michaelhany41/Garbage-Bin-/2D drawing/download.jpeg

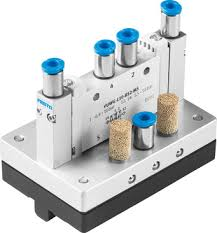
2D drawing/download.jpeg
