michaelhany41/Garbage-Bin-/SolidWorks design/Pneumatic Air Cylinder Double Action/1.jpg

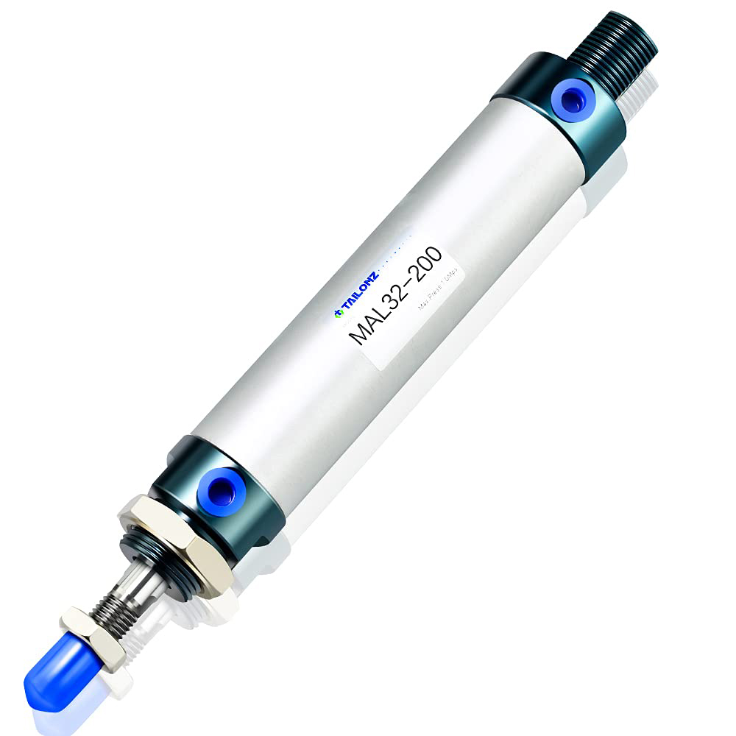
SolidWorks design/Pneumatic Air Cylinder Double Action/1.jpg
