michaelhany41/Garbage-Bin-/SolidWorks design/Pneumatic Air Cylinder Double Action/2.jpg

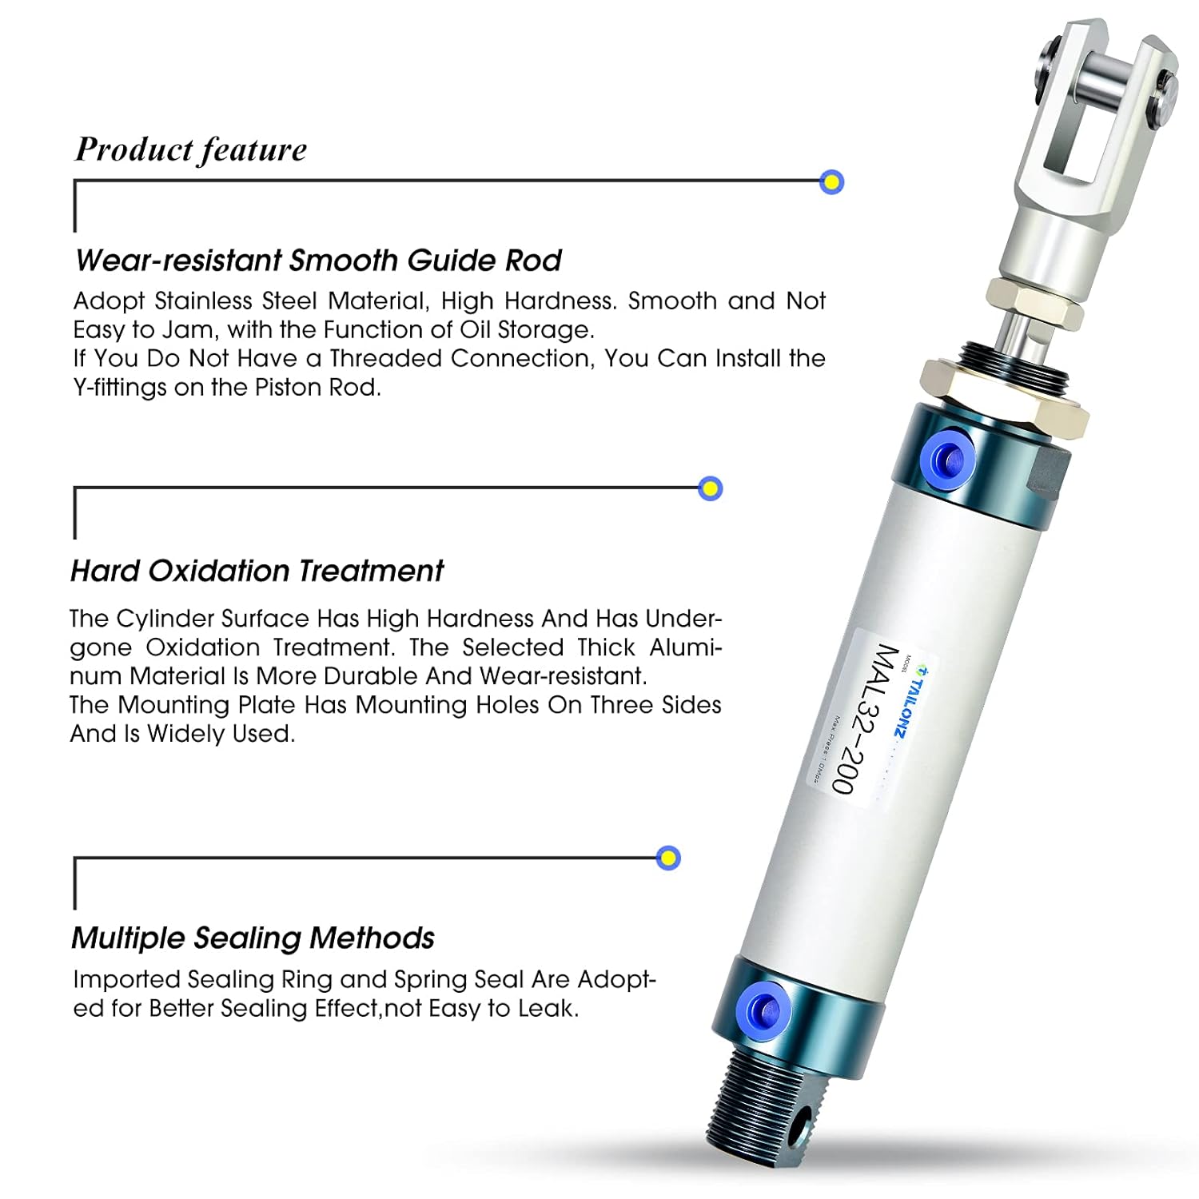
SolidWorks design/Pneumatic Air Cylinder Double Action/2.jpg
