michaelhany41/Garbage-Bin-/SolidWorks design/Assembly 1.SLDASM

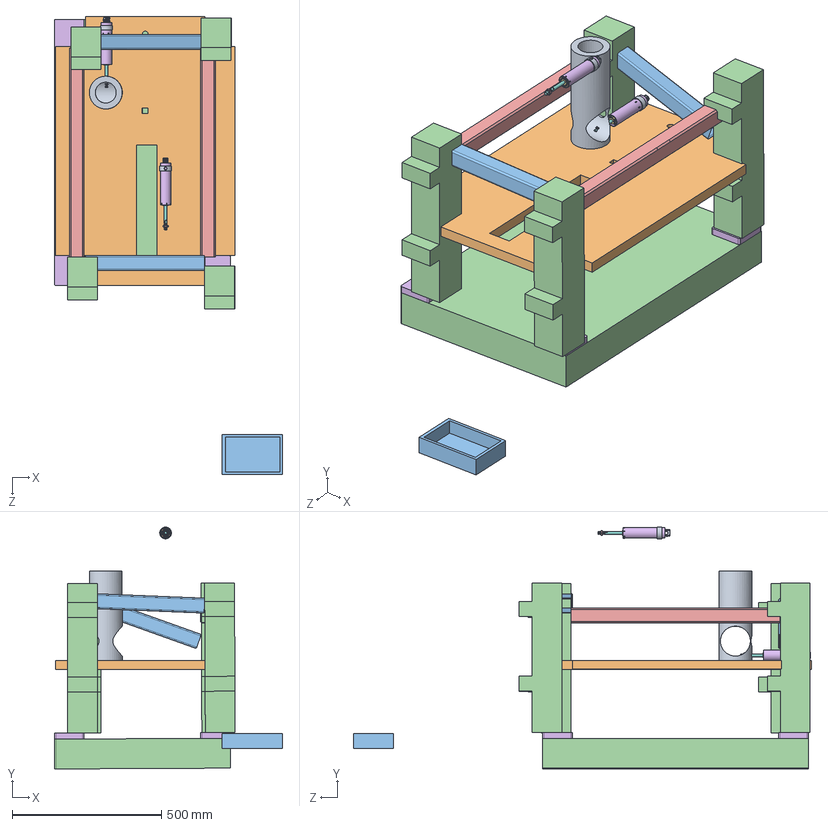
[picture p31: CAD file, 2025-08-22]
SolidWorks design/Assembly 1.SLDASM
764.2 x 809.8 x 1533.1 mm
part 7 base updated x 4
Part 4 Link 3ard tanya x 2
base el base updated
Part 8 link 3ard saghyr x 2
Hex Jam Nuts (Front Cap) x 2
Back Cap x 2
Piston Rod x 2
Front Cap x 2
Cylinder Barrel x 2
Hex Jam Nuts (Piston) x 2
supporter x 4
basket
base fo2
cupClynder
