michaelhany41/Garbage-Bin-/SolidWorks design/mini bracket.SLDPRT

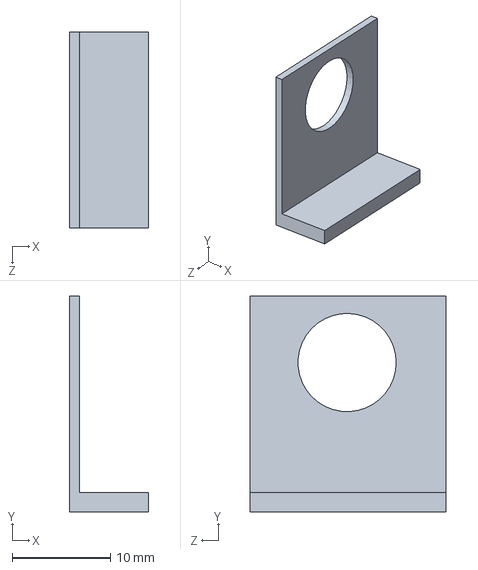
[picture p46: CAD file, 2025-08-22]
SolidWorks design/mini bracket.SLDPRT
8.00 x 22.0 x 20.0 mm
