michaelhany41/Garbage-Bin-/SolidWorks design/stand.SLDPRT

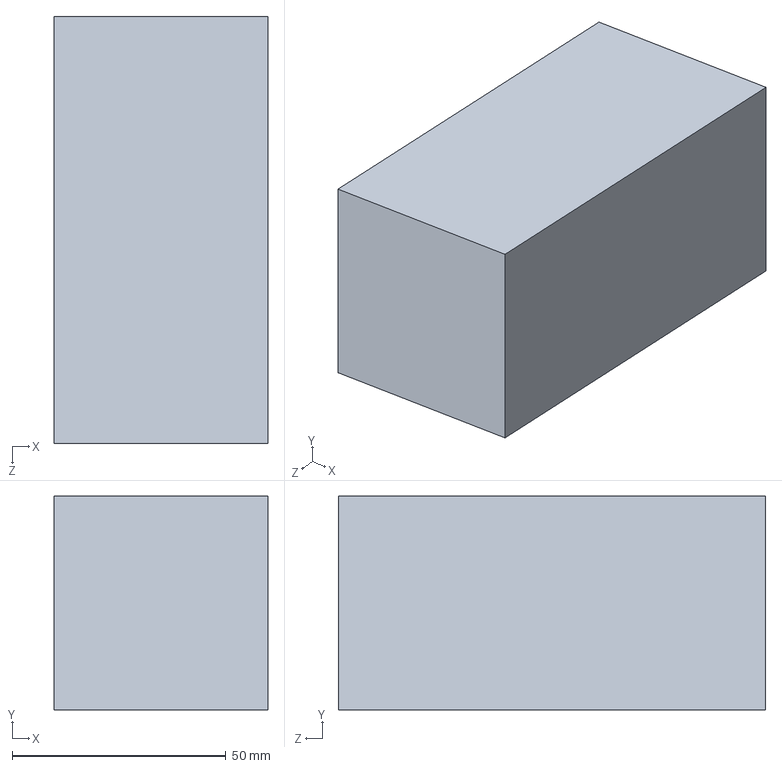
[picture p47: CAD file, 2025-08-22]
SolidWorks design/stand.SLDPRT
50.0 x 50.0 x 100.0 mm
