michaelhany41/Garbage-Bin-/SolidWorks design/Base el Base.SLDPRT

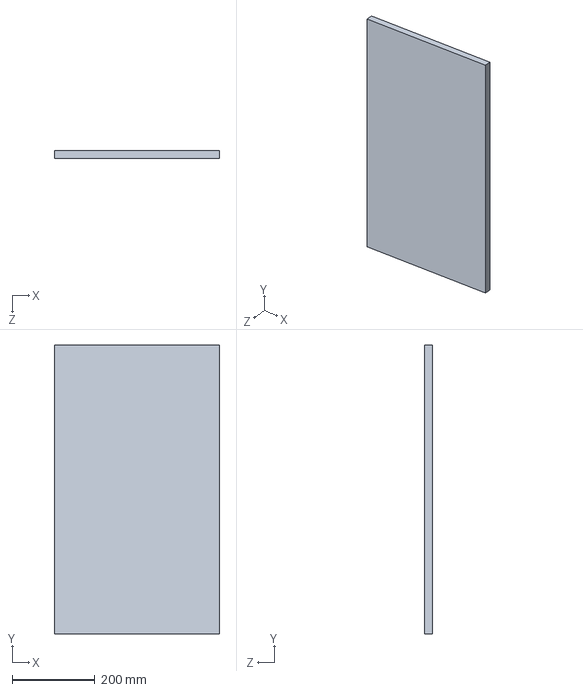
[picture p48: CAD file, 2025-08-22]
SolidWorks design/Base el Base.SLDPRT
400.0 x 700.0 x 20.0 mm
