michaelhany41/Garbage-Bin-/SolidWorks design/base fo2.SLDPRT

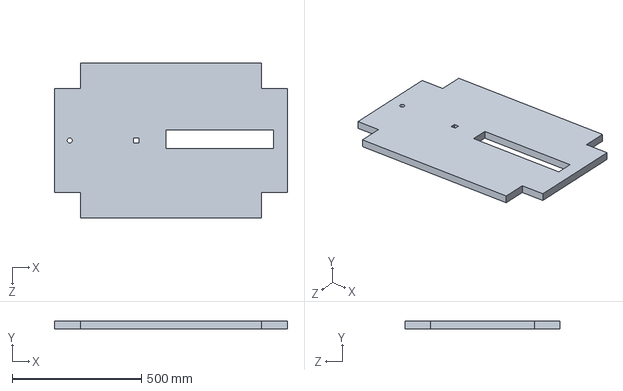
[picture p49: CAD file, 2025-08-22]
SolidWorks design/base fo2.SLDPRT
900.0 x 30.0 x 600.0 mm
