michaelhany41/Garbage-Bin-/SolidWorks design/supporter.SLDPRT

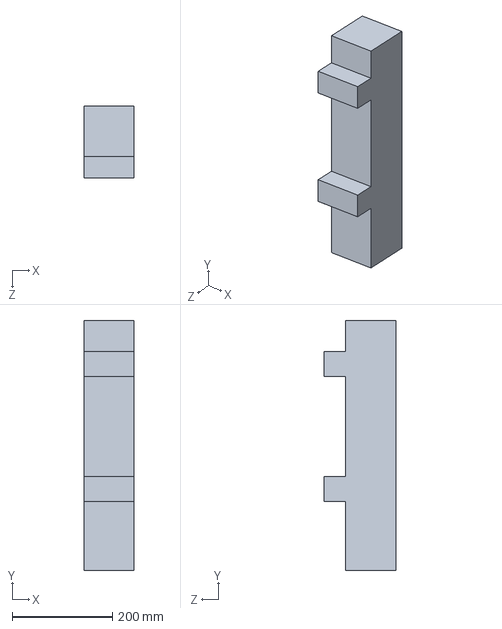
[picture p50: CAD file, 2025-08-22]
SolidWorks design/supporter.SLDPRT
100.0 x 500.0 x 143.0 mm
