michaelhany41/Garbage-Bin-/SolidWorks design/Part 8 link 3ard saghyr.SLDPRT

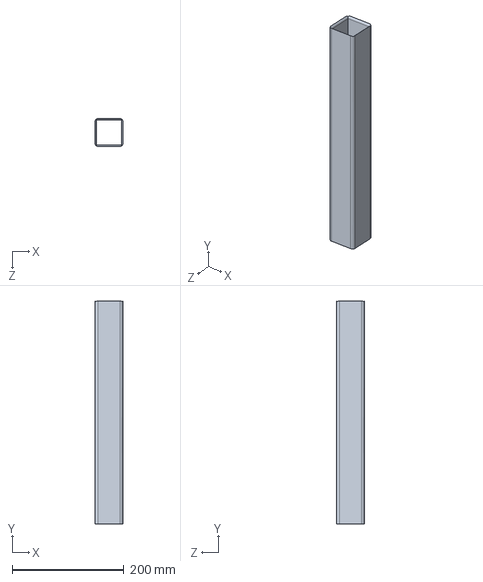
[picture p51: CAD file, 2025-08-22]
SolidWorks design/Part 8 link 3ard saghyr.SLDPRT
50.0 x 399.3 x 50.0 mm
