michaelhany41/Garbage-Bin-/SolidWorks design/ramp.SLDPRT

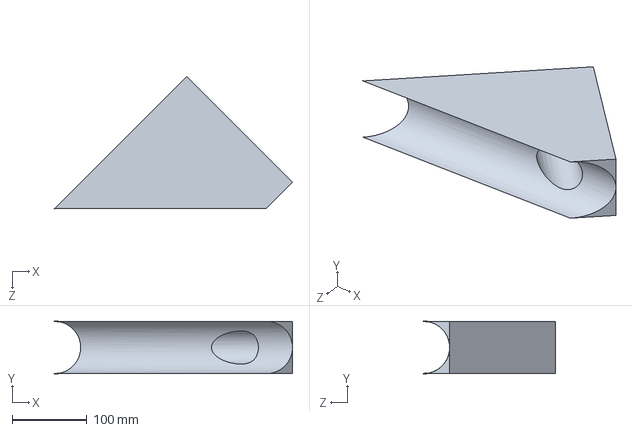
[picture p52: CAD file, 2025-08-22]
SolidWorks design/ramp.SLDPRT
318.6 x 70.0 x 176.8 mm
