michaelhany41/Garbage-Bin-/SolidWorks design/tableLeg.SLDPRT

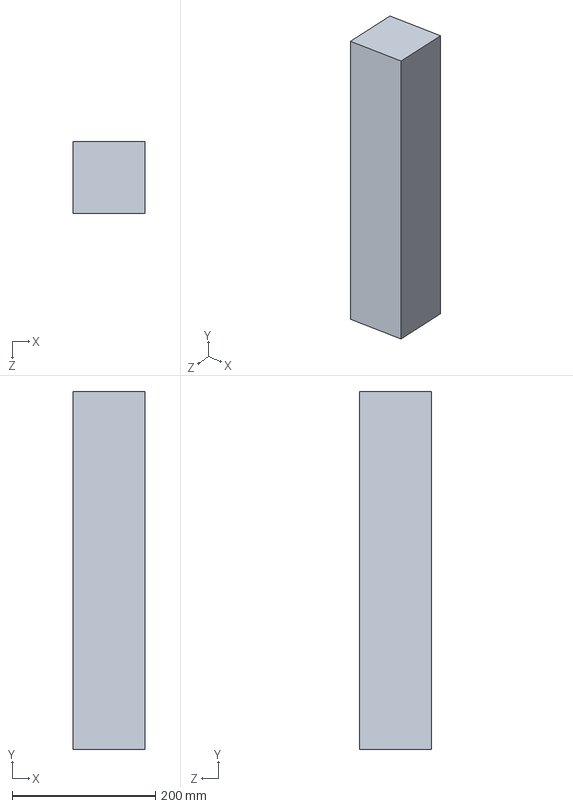
[picture p53: CAD file, 2025-08-22]
SolidWorks design/tableLeg.SLDPRT
100.0 x 500.0 x 100.0 mm
