michaelhany41/Garbage-Bin-/SolidWorks design/basket.SLDPRT

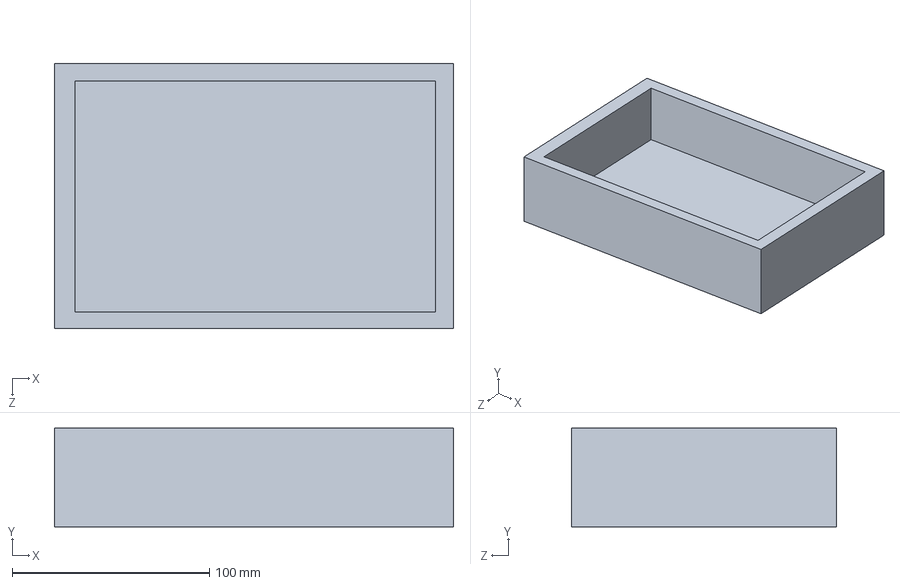
[picture p54: CAD file, 2025-08-22]
SolidWorks design/basket.SLDPRT
202.5 x 50.0 x 134.5 mm
