michaelhany41/Garbage-Bin-/SolidWorks design/Part 3 Link el 3ard.SLDPRT

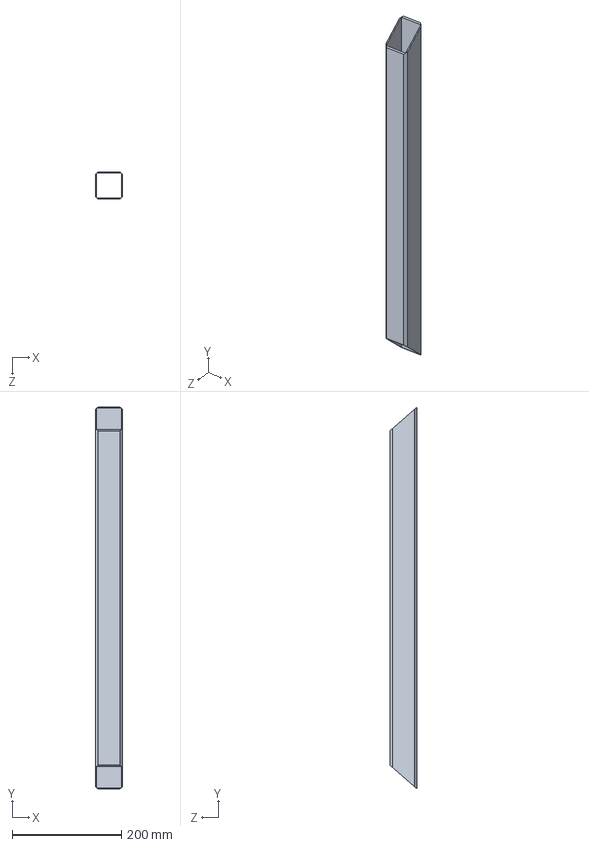
[picture p55: CAD file, 2025-08-22]
SolidWorks design/Part 3 Link el 3ard.SLDPRT
50.0 x 700.0 x 50.0 mm
