michaelhany41/Garbage-Bin-/SolidWorks design/base el base updated.SLDPRT

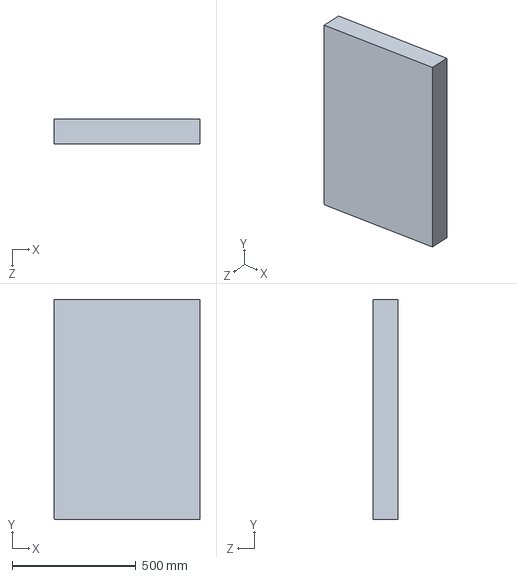
[picture p56: CAD file, 2025-08-22]
SolidWorks design/base el base updated.SLDPRT
589.3 x 890.0 x 100.0 mm
