michaelhany41/Garbage-Bin-/SolidWorks design/Part 2.SLDPRT

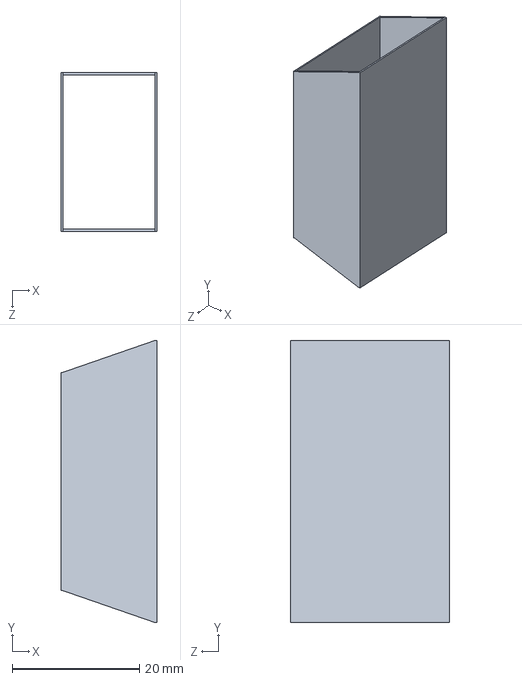
[picture p57: CAD file, 2025-08-22]
SolidWorks design/Part 2.SLDPRT
15.0 x 44.3 x 25.0 mm
