michaelhany41/Garbage-Bin-/SolidWorks design/Part 4 Link 3ard tanya.SLDPRT

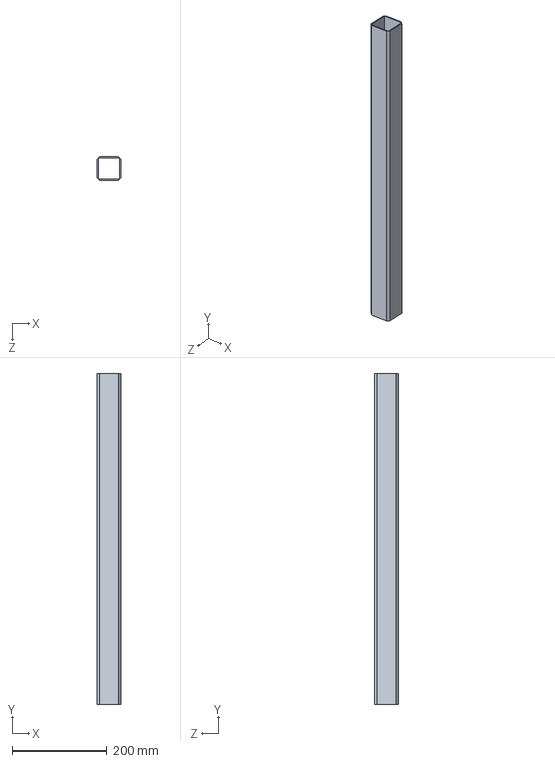
[picture p58: CAD file, 2025-08-22]
SolidWorks design/Part 4 Link 3ard tanya.SLDPRT
50.0 x 700.0 x 50.0 mm
