michaelhany41/Garbage-Bin-/SolidWorks design/cylinderHold.SLDPRT

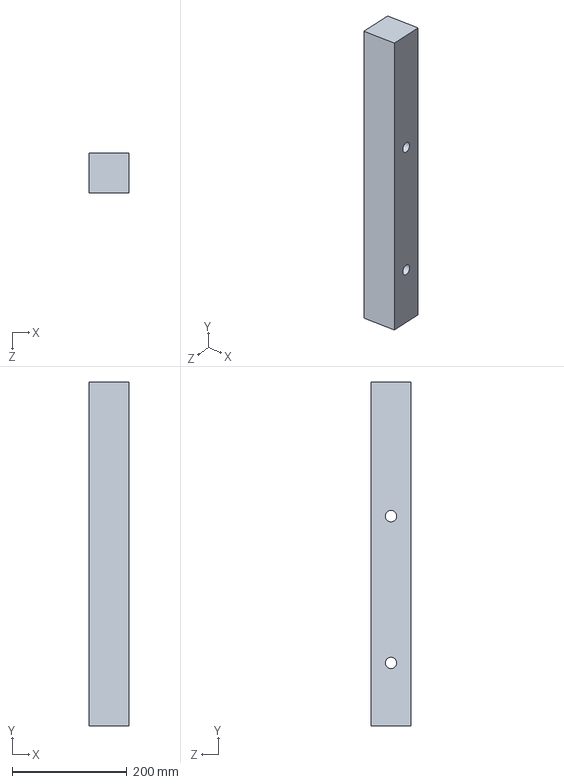
[picture p59: CAD file, 2025-08-22]
SolidWorks design/cylinderHold.SLDPRT
70.0 x 600.0 x 70.0 mm
