michaelhany41/Garbage-Bin-/SolidWorks design/part 7 base updated.SLDPRT

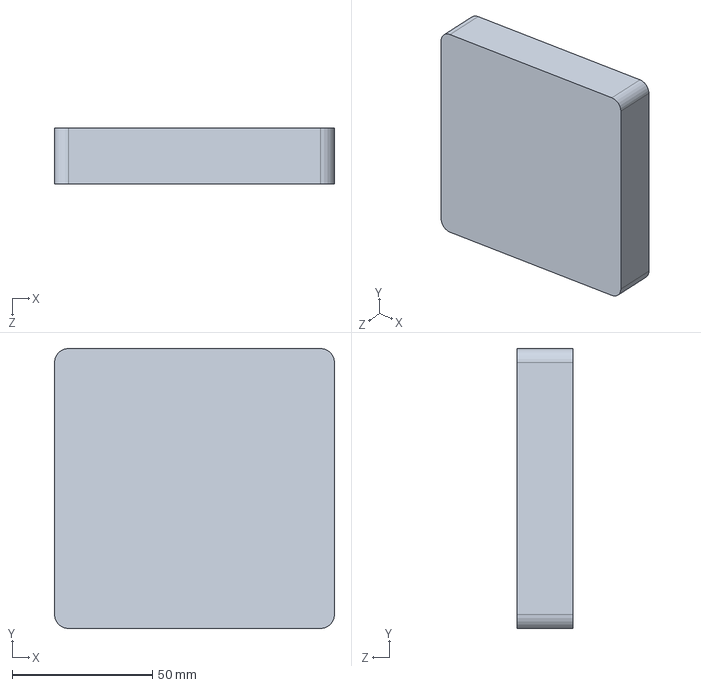
[picture p60: CAD file, 2025-08-22]
SolidWorks design/part 7 base updated.SLDPRT
100.0 x 100.0 x 20.0 mm
