michaelhany41/Garbage-Bin-/SolidWorks design/part 6.SLDPRT

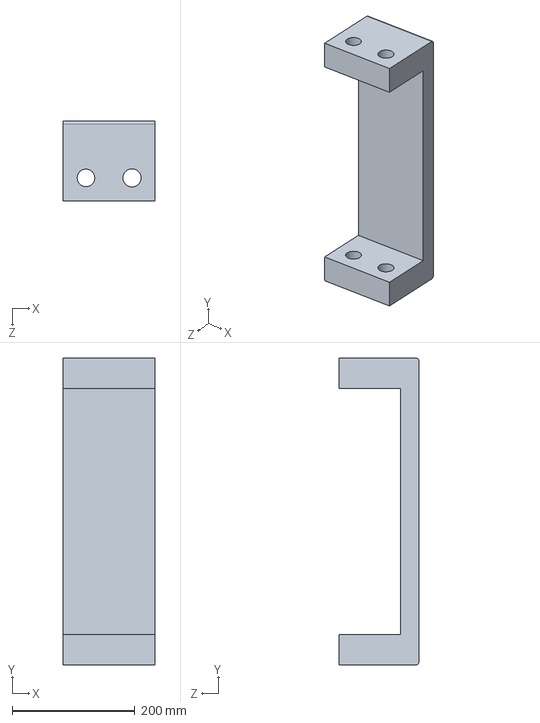
[picture p61: CAD file, 2025-08-22]
SolidWorks design/part 6.SLDPRT
150.0 x 500.0 x 130.0 mm
