michaelhany41/Garbage-Bin-/SolidWorks design/sampleCup.SLDPRT

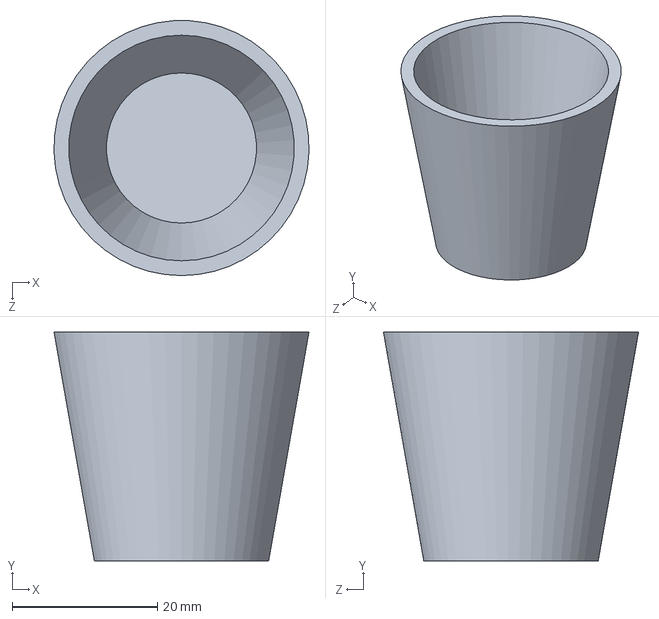
[picture p62: CAD file, 2025-08-22]
SolidWorks design/sampleCup.SLDPRT
35.1 x 31.5 x 35.1 mm
