michaelhany41/Garbage-Bin-/SolidWorks design/base level1.SLDPRT

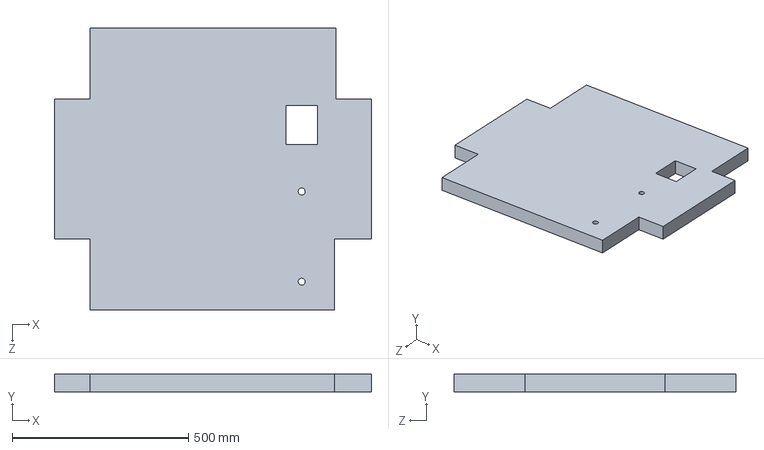
[picture p63: CAD file, 2025-08-22]
SolidWorks design/base level1.SLDPRT
900.0 x 50.0 x 800.0 mm
